asok3781/75-Keyboard/Case/midclosed.dxf

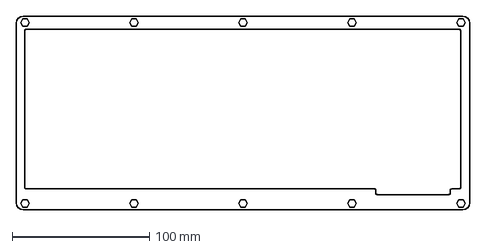
[picture p10: CAD file, 2020-07-08]
Case/midclosed.dxf
330.0 x 141.0 mm
