asok3781/75-Keyboard/Case/foot-0.dxf

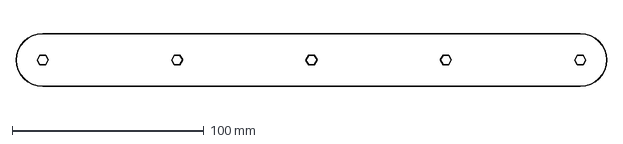
[picture p11: CAD file, 2020-07-06]
Case/foot-0.dxf
307.5 x 27.5 mm
