asok3781/75-Keyboard/Case/midclose.dxf

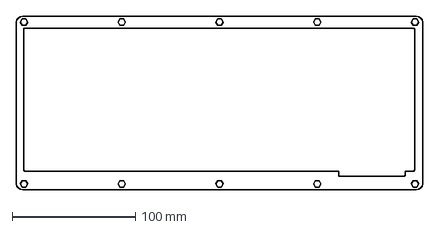
[picture p12: CAD file, 2020-07-06]
Case/midclose.dxf
330.0 x 141.0 mm
