asok3781/75-Keyboard/Case/topround.dxf

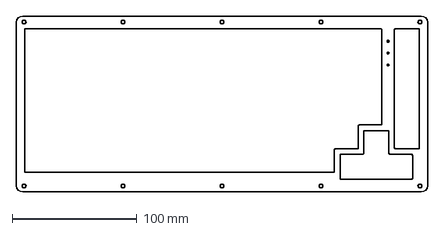
[picture p13: CAD file, 2020-07-06]
Case/topround.dxf
330.0 x 141.0 mm
